epremeaux/AVTokyo_2022_Badge/Kicad/3dmodels/AVTokyo/tact switch SMD (5.2x5.2).png

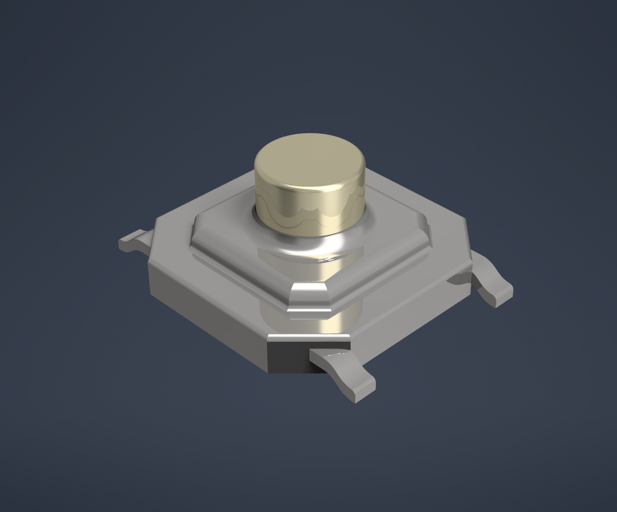
Kicad/3dmodels/AVTokyo/tact switch SMD (5.2x5.2).png
