epremeaux/AVTokyo_2022_Badge/Software/AVT2022_badge/src/MQTT_Sensors.h

#include <Arduino.h>


bool init_TempHumidity() ;
bool init_IMU() ;
void SensorsMenu_Update() ;
bool envSensor_Update();

void getMQTTsettings();
void SaveMQTTsettings();

bool MQTT_connect();
void do_MQTT_post() ;

void IMU_Update();
