epremeaux/AVTokyo_2022_Badge/Software/AVT2022_badge/src/ButtonIcons.h

/*
 * reference video: https://www.youtube.com/watch?v=wbDrjoxb51I
 *
 * use to convert: LCD Image Converter
 * settings: 
 *  Image: R5G6B5, Little-Endian / big-endian to fix color swap, block size 16 bit
 * or use gfx.setSwapBytes(true); to fix color order
 * 
 * color map: https://github.com/Bodmer/TFT_eSPI/issues/517
*/

#include <Arduino.h>
#include "AVT2022_badge_menu.h"

void ButtonTester(unsigned int encoderValue , RenderPressMode clicked);

void draw_A(int32_t posx, int32_t posy, bool pressed);
void draw_B(int32_t posx, int32_t posy, bool pressed);
void draw_Joy(int32_t posx, int32_t posy, int dir);
    //0: nothing, 1: up, 2: down, 3: left, 4: right, 5: clicked, 6: Up/Down, 7: Left/Right


/// 'icon 40x40 A button', 40x40px
const uint16_t A_button_4040 [] PROGMEM = {
0x0000, 0x0000, 0x0000, 0x0000, 0x0000, 0x0000, 0x0000, 0x0000, 0x0000, 0x0000, 0x0000, 0x0000, 0x0000, 0x1f00, 0x1f00, 0x1f00, 0x1f00, 0x1f00, 0x1f00, 0x1f00, 0x1f00, 0x1f00, 0x1f00, 0x1f00, 0x1f00, 0x1f00, 0x1f00, 0x0000, 0x0000, 0x0000, 0x0000, 0x0000, 0x0000, 0x0000, 0x0000, 0x0000, 0x0000, 0x0000, 0x0000, 0x0000, 
0x0000, 0x0000, 0x0000, 0x0000, 0x0000, 0x0000, 0x0000, 0x0000, 0x0000, 0x0000, 0x0000, 0x1f00, 0x1f00, 0x1f00, 0x1f00, 0x1f00, 0x1f00, 0x1f00, 0x1f00, 0x1f00, 0x1f00, 0x1f00, 0x1f00, 0x1f00, 0x1f00, 0x1f00, 0x1f00, 0x1f00, 0x1f00, 0x0000, 0x0000, 0x0000, 0x0000, 0x0000, 0x0000, 0x0000, 0x0000, 0x0000, 0x0000, 0x0000, 
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
};
