epremeaux/AVTokyo_2022_Badge/Software/AVT2022_badge/src/ndnh277.h

// array size is 31423
static const unsigned char ndnh277[] PROGMEM  = {
  0x89, 0x50, 0x4e, 0x47, 0x0d, 0x0a, 0x1a, 0x0a, 0x00, 0x00, 0x00, 0x0d, 0x49, 0x48, 0x44, 0x52, 
  0x00, 0x00, 0x00, 0xf0, 0x00, 0x00, 0x01, 0x18, 0x08, 0x02, 0x00, 0x00, 0x00, 0xed, 0x57, 0xec, 
  0x9e, 0x00, 0x00, 0x00, 0x01, 0x73, 0x52, 0x47, 0x42, 0x00, 0xae, 0xce, 0x1c, 0xe9, 0x00, 0x00, 
  0x00, 0x04, 0x67, 0x41, 0x4d, 0x41, 0x00, 0x00, 0xb1, 0x8f, 0x0b, 0xfc, 0x61, 0x05, 0x00, 0x00, 
  0x00, 0x09, 0x70, 0x48, 0x59, 0x73, 0x00, 0x00, 0x16, 0x25, 0x00, 0x00, 0x16, 0x25, 0x01, 0x49, 
  0x52, 0x24, 0xf0, 0x00, 0x00, 0x7a, 0x54, 0x49, 0x44, 0x41, 0x54, 0x78, 0x5e, 0xed, 0x9d, 0x05, 
  0x7c, 0xd5, 0xd6, 0xdf, 0xc6, 0x53, 0xf7, 0xd2, 0x16, 0x4a, 0x91, 0xe2, 0x36, 0x7c, 0xb8, 0xc3, 
  0x70, 0x77, 0x77, 0x8a, 0xbb, 0xbb, 0x3b, 0x85, 0x22, 0x45, 0x6a, 0xb4, 0x40, 0xd1, 0xb2, 0x0d, 
  0x87, 0x0d, 0xd7, 0x52, 0x7c, 0xd8, 0x06, 0x63, 0xc8, 0x60, 0xc8, 0x06, 0x0c, 0xb7, 0x21, 0x1b, 
  0x7d, 0xbf, 0xb9, 0xbf, 0xee, 0xbc, 0xf7, 0xdf, 0x96, 0x0e, 0x87, 0xb1, 0x3c, 0x9f, 0x12, 0x4e, 
  0x4e, 0x4e, 0x4e, 0x72, 0x73, 0xbe, 0xe7, 0x97, 0xe7, 0x24, 0xb9, 0xb9, 0x9a, 0x21, 0x43, 0x86, 
  0x0c, 0xfd, 0xb3, 0xec, 0xec, 0xec, 0x2c, 0x2c, 0x2c, 0x2c, 0x4d, 0x8a, 0xc9, 0x32, 0xc9, 0xde, 
  0xde, 0x9e, 0xfc, 0x98, 0x19, 0x43, 0x86, 0xde, 0xbf, 0x84, 0x4b, 0x2b, 0x2b, 0x2b, 0xeb, 0xf8, 
  0x14, 0x53, 0x28, 0x8e, 0x00, 0xd7, 0xc1, 0xc1, 0xc1, 0xd1, 0xd1, 0x51, 0x66, 0xd3, 0xa7, 0x4f, 
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
  0xcc, 0x44, 0x68, 0x68, 0x06, 0x41, 0x12, 0x26, 0x20, 0x5f, 0x0d, 0x68, 0xca, 0x8b, 0x63, 0x51, 
  0x92, 0x7a, 0xa4, 0x66, 0xe0, 0x3e, 0x7f, 0xfe, 0x7c, 0x68, 0x68, 0x68, 0xc2, 0x36, 0xc6, 0x90, 
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
};
