epremeaux/AVTokyo_2022_Badge/Software/AVT2022_badge/src/BatteryWidget25x15.h

#include <PlatformDetermination.h>
// https://www.thecoderscorner.com/products/arduino-libraries/tc-menu/rendering-with-tcmenu-lcd-tft-oled/

// icons are 15 x 25

const uint8_t batteryZero[] PROGMEM = {
    0xe0, 0x03, 0x10, 0x04, 0x1e, 0x3c, 0x01, 0x40, 0x01, 0x40, 0x01, 0x40,
   0xff, 0x7f, 0x01, 0x40, 0x01, 0x40, 0x01, 0x40, 0x01, 0x40, 0x01, 0x40,
   0xff, 0x7f, 0x01, 0x40, 0x01, 0x40, 0x01, 0x40, 0x01, 0x40, 0x01, 0x40,
   0xff, 0x7f, 0x01, 0x40, 0x01, 0x40, 0x01, 0x40, 0x01, 0x40, 0x01, 0x40,
   0xfe, 0x3f
};


const uint8_t batteryTwentyFive[] PROGMEM = {
   0xe0, 0x03, 0x10, 0x04, 0x1e, 0x3c, 0x01, 0x40, 0x01, 0x40, 0x01, 0x40,
   0xff, 0x7f, 0x01, 0x40, 0x01, 0x40, 0x01, 0x40, 0x01, 0x40, 0x01, 0x40,
   0xff, 0x7f, 0x01, 0x40, 0x01, 0x40, 0x01, 0x40, 0x01, 0x40, 0x01, 0x40,
   0xff, 0x7f, 0x01, 0x40, 0xfd, 0x5f, 0xfd, 0x5f, 0xfd, 0x5f, 0x01, 0x40,
   0xfe, 0x3f
};

const uint8_t batteryFifty[] PROGMEM = {
    0xe0, 0x03, 0x10, 0x04, 0x1e, 0x3c, 0x01, 0x40, 0x01, 0x40, 0x01, 0x40,
   0xff, 0x7f, 0x01, 0x40, 0x01, 0x40, 0x01, 0x40, 0x01, 0x40, 0x01, 0x40,
   0xff, 0x7f, 0x01, 0x40, 0xfd, 0x5f, 0xfd, 0x5f, 0xfd, 0x5f, 0x01, 0x40,
   0xff, 0x7f, 0x01, 0x40, 0xfd, 0x5f, 0xfd, 0x5f, 0xfd, 0x5f, 0x01, 0x40,
   0xfe, 0x3f
};

const uint8_t batterySeventyFive[] PROGMEM = {
   0xe0, 0x03, 0x10, 0x04, 0x1e, 0x3c, 0x01, 0x40, 0x01, 0x40, 0x01, 0x40,
   0xff, 0x7f, 0x01, 0x40, 0xfd, 0x5f, 0xfd, 0x5f, 0xfd, 0x5f, 0x01, 0x40,
   0xff, 0x7f, 0x01, 0x40, 0xfd, 0x5f, 0xfd, 0x5f, 0xfd, 0x5f, 0x01, 0x40,
   0xff, 0x7f, 0x01, 0x40, 0xfd, 0x5f, 0xfd, 0x5f, 0xfd, 0x5f, 0x01, 0x40,
   0xfe, 0x3f
};

const uint8_t batteryOneHundred[] PROGMEM = {
    0xe0, 0x03, 0x10, 0x04, 0xde, 0x3d, 0xc1, 0x41, 0xfd, 0x5f, 0x01, 0x40,
   0xff, 0x7f, 0x01, 0x40, 0xfd, 0x5f, 0xfd, 0x5f, 0xfd, 0x5f, 0x01, 0x40,
   0xff, 0x7f, 0x01, 0x40, 0xfd, 0x5f, 0xfd, 0x5f, 0xfd, 0x5f, 0x01, 0x40,
   0xff, 0x7f, 0x01, 0x40, 0xfd, 0x5f, 0xfd, 0x5f, 0xfd, 0x5f, 0x01, 0x40,
   0xfe, 0x3f
};


const uint8_t* const iconsBattery[] PROGMEM = { batteryZero, batteryTwentyFive, batteryFifty, batterySeventyFive, batteryOneHundred };
