epremeaux/AVTokyo_2022_Badge/Software/AVT2022_badge/src/scanner.h

#include <Arduino.h>
#include "AVT2022_badge_menu.h"

void new_WiFi_scan(unsigned int encoderValue , RenderPressMode clicked) ;

void new_Bluetooth_scan(unsigned int encoderValue , RenderPressMode clicked)  ;
